mbovero/Vizzy_Senior_Project/docs/CAD/screenshots/20Kg Servo Bracket v6.jpg

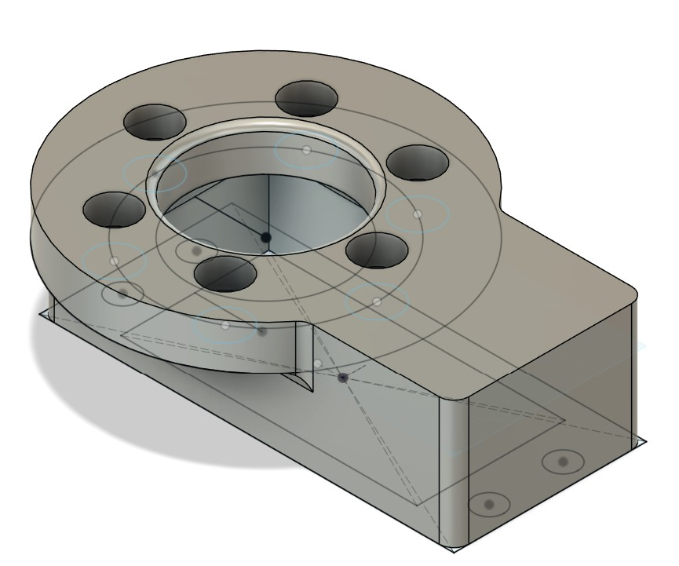
docs/CAD/screenshots/20Kg Servo Bracket v6.jpg
