mbovero/Vizzy_Senior_Project/docs/CAD/screenshots/UpperArm.jpg

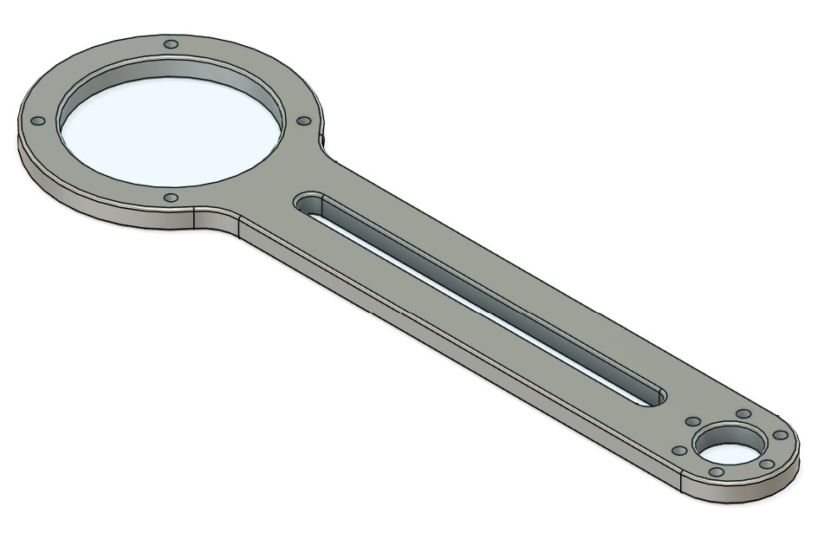
docs/CAD/screenshots/UpperArm.jpg
