mbovero/Vizzy_Senior_Project/docs/diagrams/Higher_Level_Diagram.png

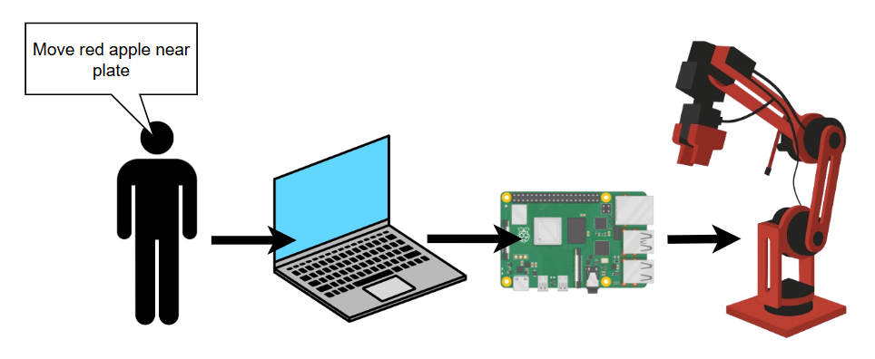
docs/diagrams/Higher_Level_Diagram.png
