mbovero/Vizzy_Senior_Project/docs/images/ArmExtended.jpeg

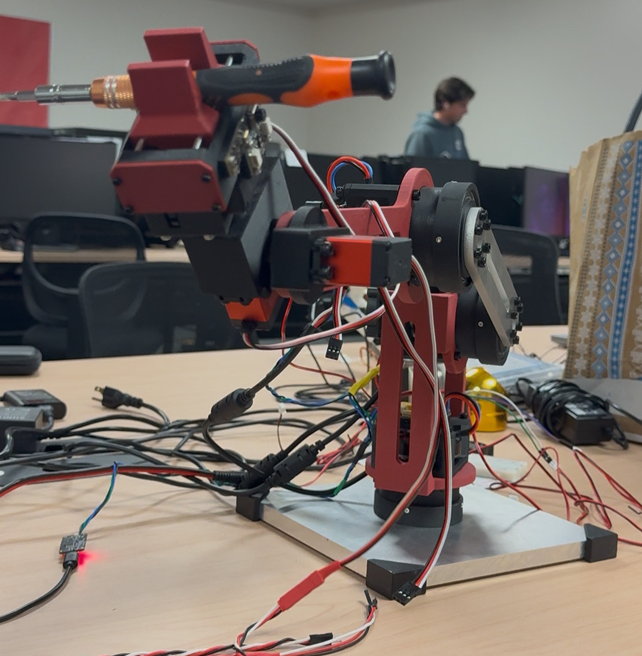
docs/images/ArmExtended.jpeg
