mbovero/Vizzy_Senior_Project/docs/images/base_f.jpg

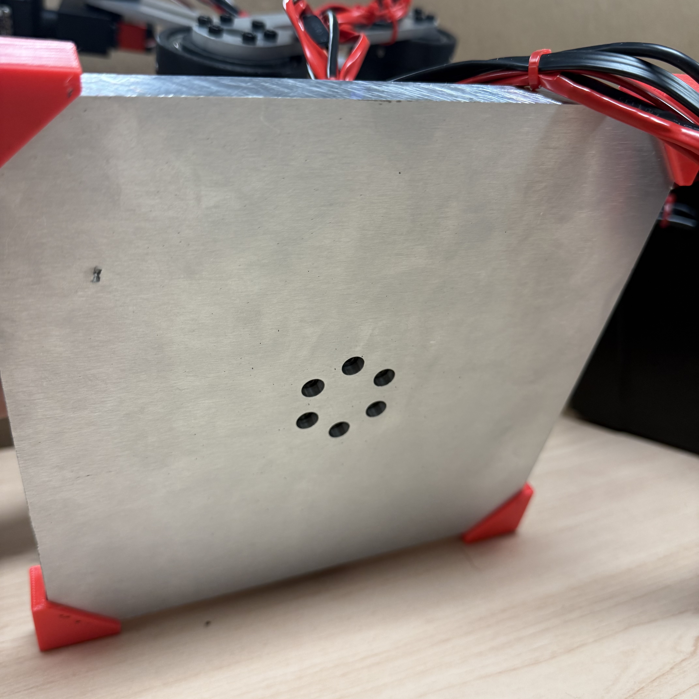
docs/images/base_f.jpg
