mbovero/Vizzy_Senior_Project/docs/images/Fan Bracket v2.jpg

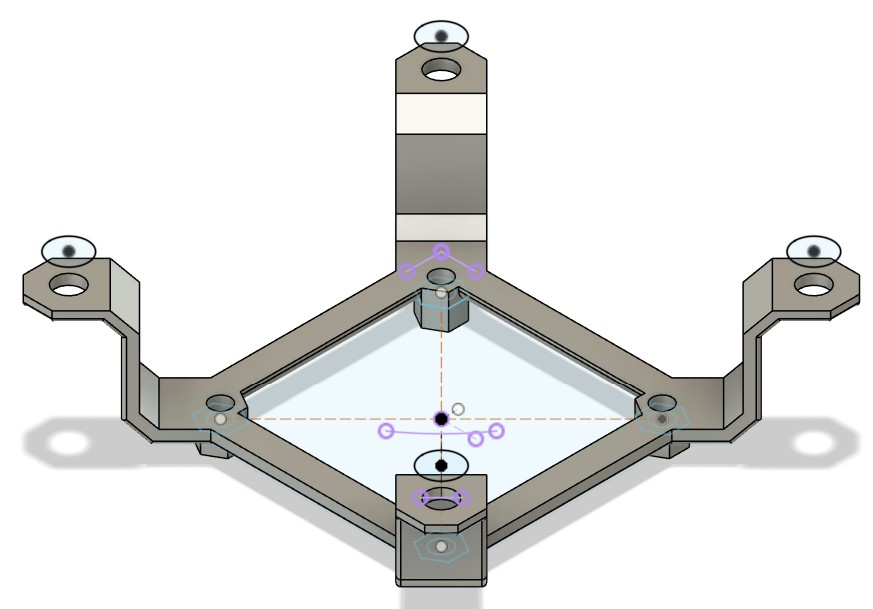
docs/images/Fan Bracket v2.jpg
