mbovero/Vizzy_Senior_Project/docs/images/gripper.jpg

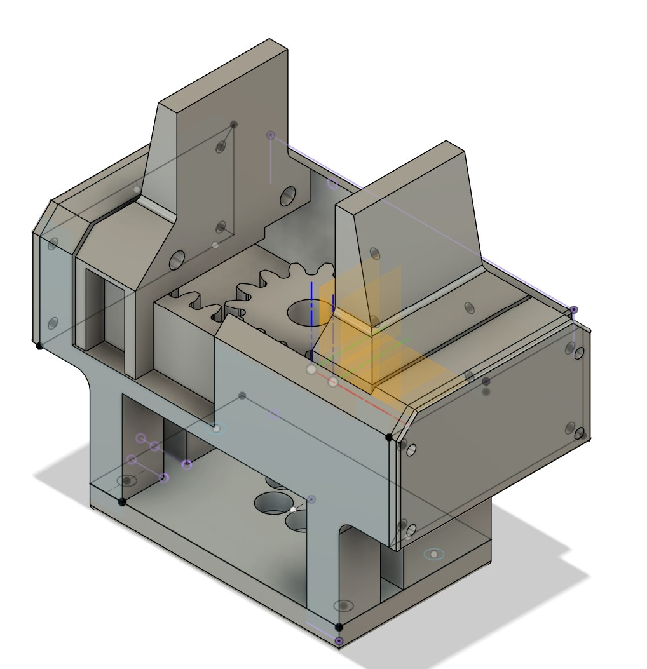
docs/images/gripper.jpg
