mbovero/Vizzy_Senior_Project/docs/images/GripperHolding.jpg

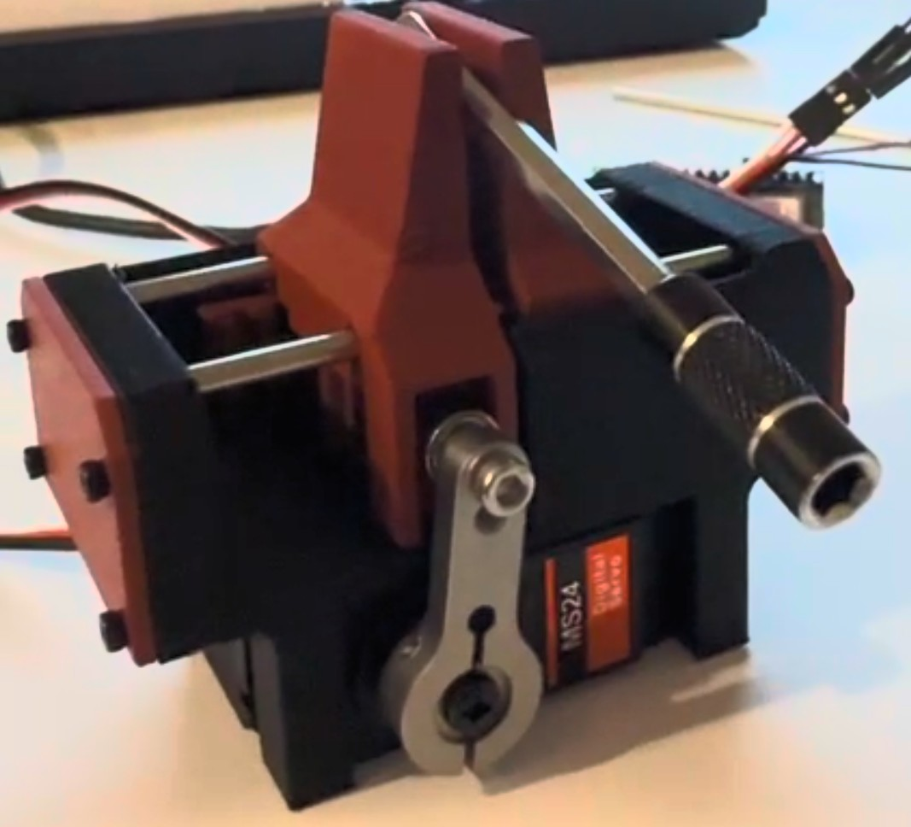
docs/images/GripperHolding.jpg
