mbovero/Vizzy_Senior_Project/docs/images/m_joint_f.jpg

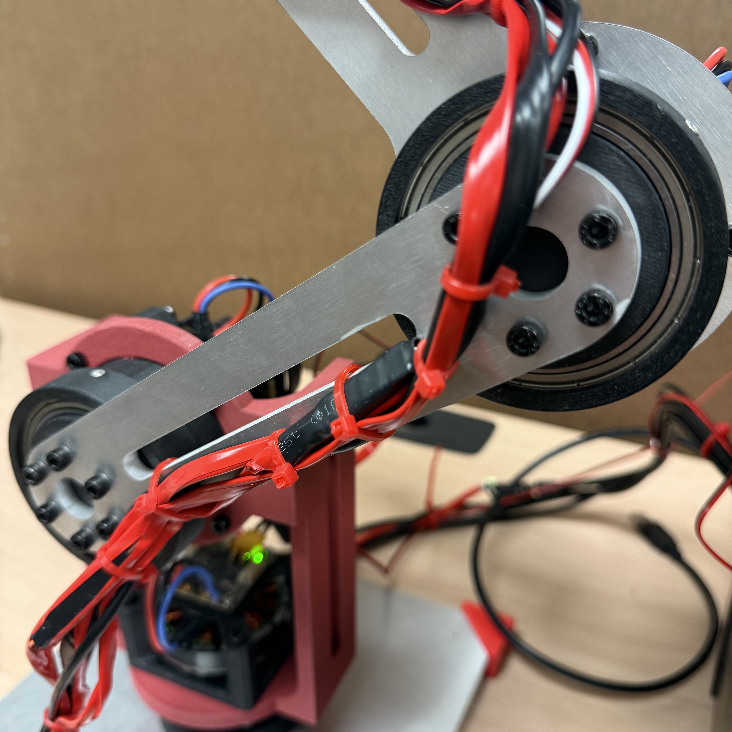
docs/images/m_joint_f.jpg
