mbovero/Vizzy_Senior_Project/software/LLM/glass bottle.jpg

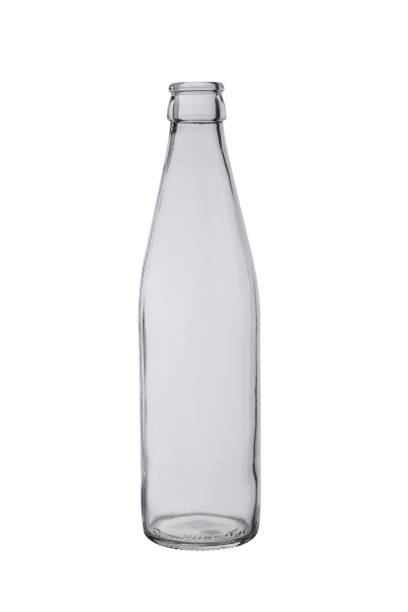
software/LLM/glass bottle.jpg
