mbovero/Vizzy_Senior_Project/software/LLM/two_bottles.jpg

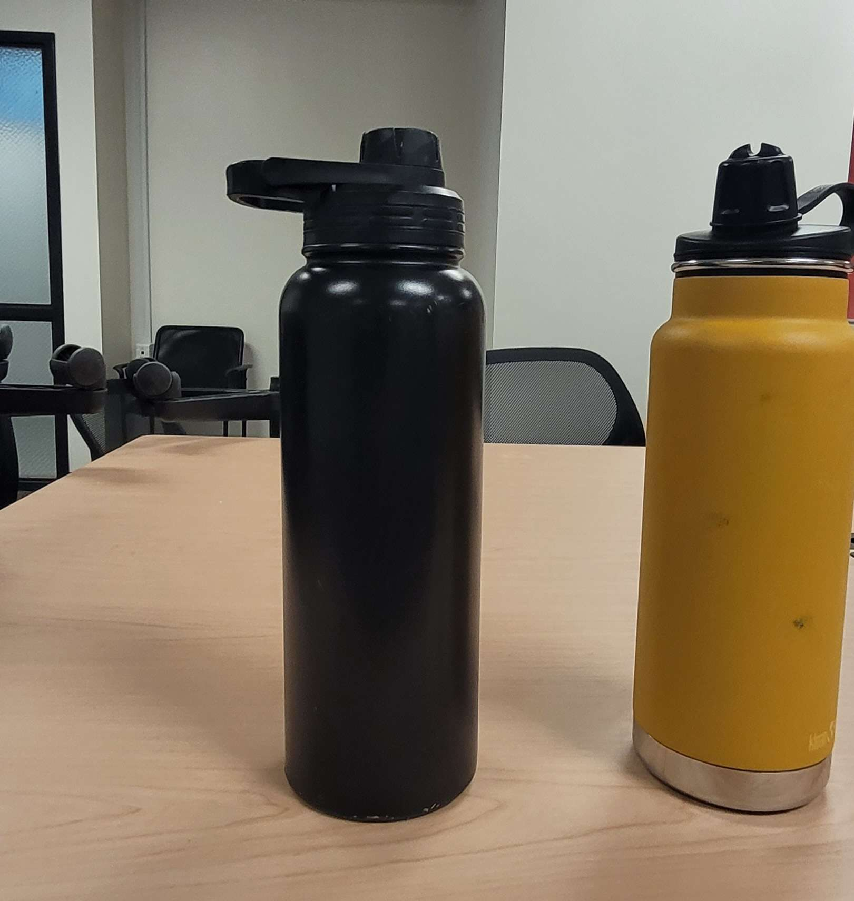
software/LLM/two_bottles.jpg
