mbovero/Vizzy_Senior_Project/software/LLM/white mug.png

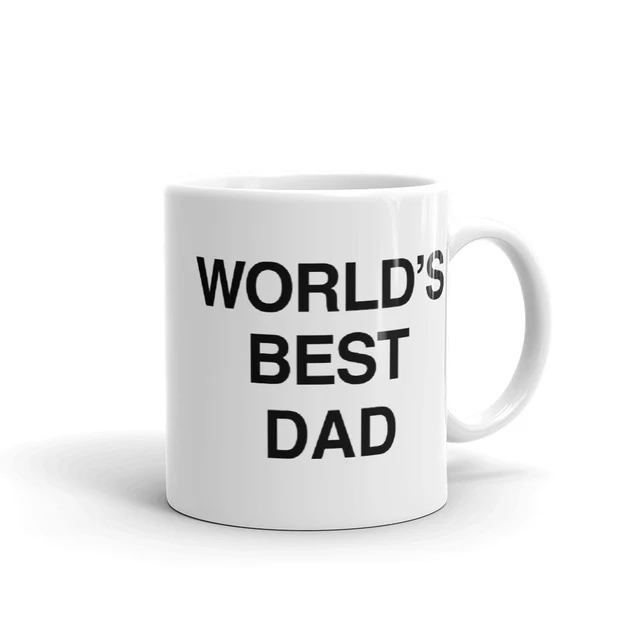
software/LLM/white mug.png
